v9938/md2mini2usb/PCB/MD2mini2USB_SCH.png

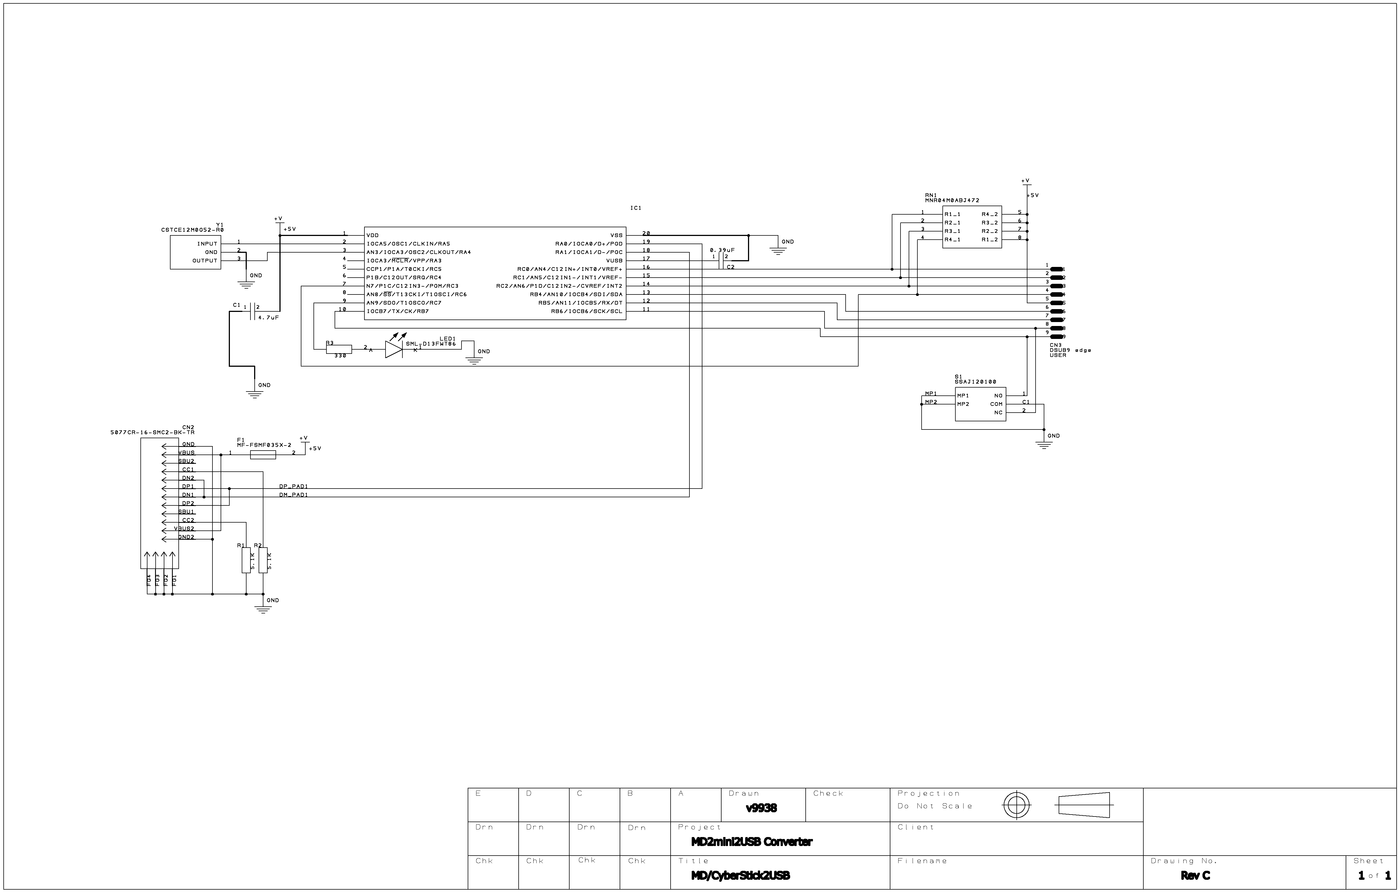
PCB/MD2mini2USB_SCH.png
