v9938/md2mini2usb/PCB/PCBBOTTOM.png

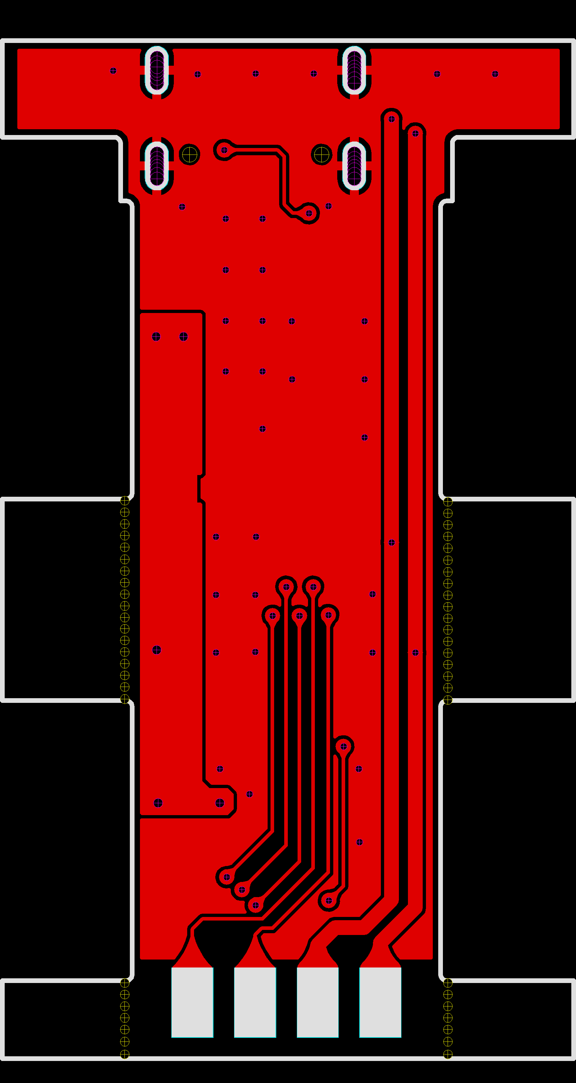
PCB/PCBBOTTOM.png
