v9938/md2mini2usb/PCB/PCBTOP.png

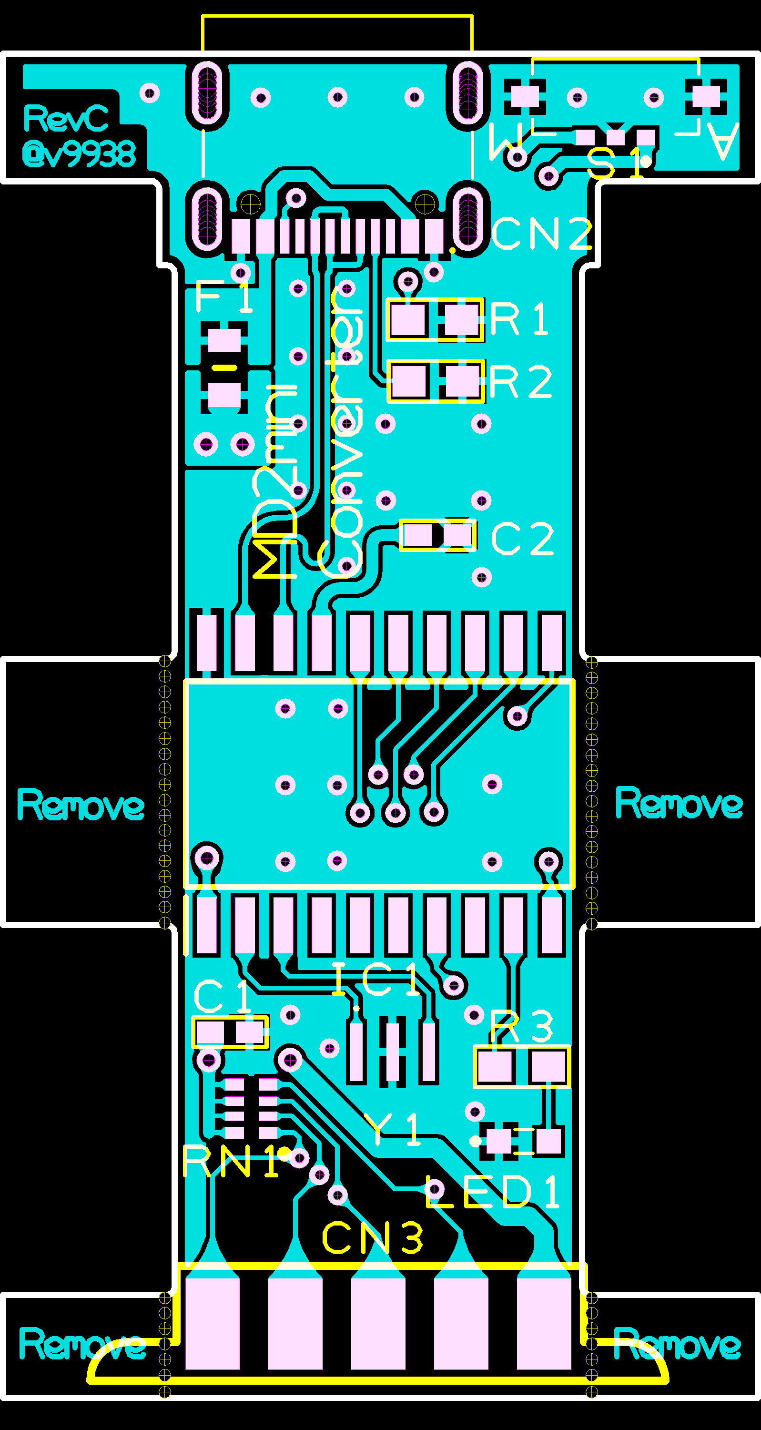
PCB/PCBTOP.png
