v9938/md2mini2usb/firmware/forMDmini/v2017_03_06/apps/usb/device/hid_joystick-segamd2/firmware/src/system_config/pic18f14k50_userboard/adc.h

/********************************************************************
 Software License Agreement:

 The software supplied herewith by Microchip Technology Incorporated
 (the "Company") for its PIC(R) Microcontroller is intended and
 supplied to you, the Company's customer, for use solely and
 exclusively on Microchip PIC Microcontroller products. The
 software is owned by the Company and/or its supplier, and is
 protected under applicable copyright laws. All rights are reserved.
 Any use in violation of the foregoing restrictions may subject the
 user to criminal sanctions under applicable laws, as well as to
 civil liability for the breach of the terms and conditions of this
 license.

 THIS SOFTWARE IS PROVIDED IN AN "AS IS" CONDITION. NO WARRANTIES,
 WHETHER EXPRESS, IMPLIED OR STATUTORY, INCLUDING, BUT NOT LIMITED
 TO, IMPLIED WARRANTIES OF MERCHANTABILITY AND FITNESS FOR A
 PARTICULAR PURPOSE APPLY TO THIS SOFTWARE. THE COMPANY SHALL NOT,
 IN ANY CIRCUMSTANCES, BE LIABLE FOR SPECIAL, INCIDENTAL OR
 CONSEQUENTIAL DAMAGES, FOR ANY REASON WHATSOEVER.
 *******************************************************************/

#ifndef ADC_H
#define ADC_H

#include <stdint.h>
#include <stdbool.h>

/*** ADC Channel Definitions *****************************************/
#define ADC_CHANNEL_POTENTIOMETER ADC_CHANNEL_10

typedef enum
{
    ADC_CHANNEL_10 = 10,
} ADC_CHANNEL;

typedef enum
{
    ADC_CONFIGURATION_DEFAULT
} ADC_CONFIGURATION;

/*********************************************************************
* Function: ADC_ReadPercentage(ADC_CHANNEL channel);
*
* Overview: Reads the requested ADC channel and returns the percentage
*            of that conversions result (0-100%).
*
* PreCondition: channel is enabled via ADC_Enable()
*
* Input: ADC_CHANNEL channel - enumeration of the ADC channels
*        available in this demo.  They should be meaningful names and
*        not the names of the ADC pins on the device (as the demo code
*        may be ported to other boards).
*         i.e. ADC_ReadPercentage(ADC_CHANNEL_POTENTIOMETER);
*
* Output: uint8_t indicating the percentage of the result 0-100% or
*         0xFF for an error
*
********************************************************************/
uint8_t ADC_ReadPercentage(ADC_CHANNEL channel);


/*********************************************************************
* Function: ADC_Read10bit(ADC_CHANNEL channel);
*
* Overview: Reads the requested ADC channel and returns the 10-bit
*           representation of this data.
*
* PreCondition: channel is enabled via ADC_Enable()
*
* Input: ADC_CHANNEL channel - enumeration of the ADC channels
*        available in this demo.  They should be meaningful names and
*        not the names of the ADC pins on the device (as the demo code
*        may be ported to other boards).
*         i.e. - ADCReadPercentage(ADC_CHANNEL_POTENTIOMETER);
*
* Output: uint16_t the right adjusted 10-bit representation of the ADC
*         channel conversion or 0xFFFF for an error.
*
********************************************************************/
uint16_t ADC_Read10bit(ADC_CHANNEL channel);

/*********************************************************************
* Function: bool ADC_Enable(ADC_CHANNEL channel, ADC_CONFIGURATION configuration);
*
* Overview: Enables specified channel
*
* PreCondition: none
*
* Input: ADC_CHANNEL channel - the channel to enable
*
* Output: bool - true if successfully configured.  false otherwise.
*
********************************************************************/
bool ADC_Enable(ADC_CHANNEL channel);

/*********************************************************************
* Function: bool ADC_SetConfiguration(ADC_CONFIGURATION configuration)
*
* Overview: Configures the ADC module to specified setting
*
* PreCondition: none
*
* Input: ADC_CONFIGURATION configuration - the mode in which to run the ADC
*
* Output: bool - true if successfully configured.  false otherwise.
*
********************************************************************/
bool ADC_SetConfiguration(ADC_CONFIGURATION configuration);

#endif  //ADC_H
